yoavg914/Smart-Spinner/KiCad_files/2ND_PCB/10_LED_ARM.kicad_sch

## KiCad design KiCad_files/2ND_PCB/10_LED_ARM.kicad_sch (2025-07-11)

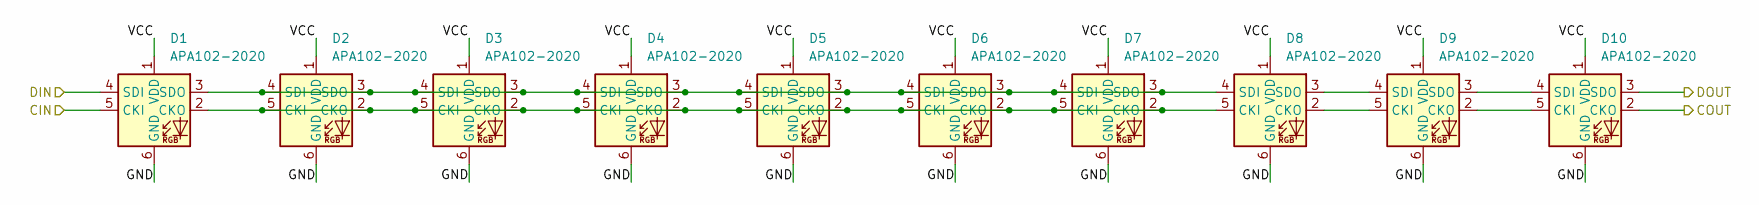
[picture p25: schematic 10_LED_ARM.kicad_sch]

Parts:
D1, D2, D3, D4, D5, D6, D7, D8, D9, D10: APA102-2020; LED-APA102-2020

Connections:
CIN: D1.5 (CKI)
COUT: D10.2 (CKO)
DIN: D1.4 (SDI)
DOUT: D10.3 (SDO)
GND: D1.6 (GND), D2.6 (GND), D3.6 (GND), D4.6 (GND), D5.6 (GND), D6.6 (GND), D7.6 (GND), D8.6 (GND), D9.6 (GND), D10.6 (GND)
unnamed: D1.2 (CKO), D2.2 (CKO), D2.5 (CKI), D3.2 (CKO), D3.5 (CKI), D4.2 (CKO), D4.5 (CKI), D5.2 (CKO), D5.5 (CKI), D6.2 (CKO), D6.5 (CKI), D7.2 (CKO), D7.5 (CKI), D8.5 (CKI)
unnamed: D1.3 (SDO), D2.3 (SDO), D2.4 (SDI), D3.3 (SDO), D3.4 (SDI), D4.3 (SDO), D4.4 (SDI), D5.3 (SDO), D5.4 (SDI), D6.3 (SDO), D6.4 (SDI), D7.3 (SDO), D7.4 (SDI), D8.4 (SDI)
unnamed: D8.2 (CKO), D9.5 (CKI)
unnamed: D8.3 (SDO), D9.4 (SDI)
unnamed: D9.3 (SDO), D10.4 (SDI)
unnamed: D9.2 (CKO), D10.5 (CKI)
VCC: D1.1 (VDD), D2.1 (VDD), D3.1 (VDD), D4.1 (VDD), D5.1 (VDD), D6.1 (VDD), D7.1 (VDD), D8.1 (VDD), D9.1 (VDD), D10.1 (VDD)
