yoavg914/Smart-Spinner/KiCad_files/2ND_PCB/LOWER_PCB_CONNECTORS.kicad_sch

## KiCad design KiCad_files/2ND_PCB/LOWER_PCB_CONNECTORS.kicad_sch (2025-07-11)

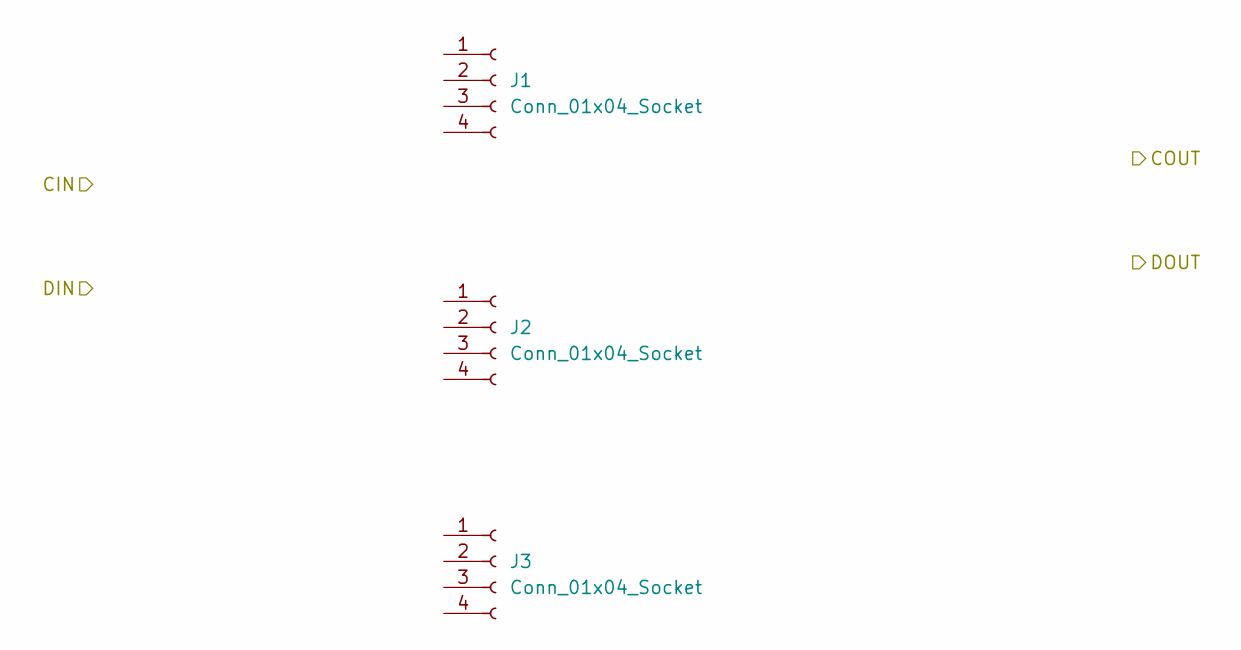
[picture p26: schematic LOWER_PCB_CONNECTORS.kicad_sch]

Parts:
J1, J2, J3: Conn_01x04_Socket
